fardog/anton/src/strings.h

#ifndef strings_h
#define strings_h

extern const char *serverIndex;
extern const char *serverUnconfigured;
extern const char *calibrationPage;
extern const char *calibrationResultPage;
extern const char *resetPage;

#endif
